Makerfabs/ESP32-S3-Parallel-TFT-with-Touch-4.3inch/examples/ESP-IDF/matouch/components/lvgl__lvgl/docs/src/_static/images/renesas/toolchains.png

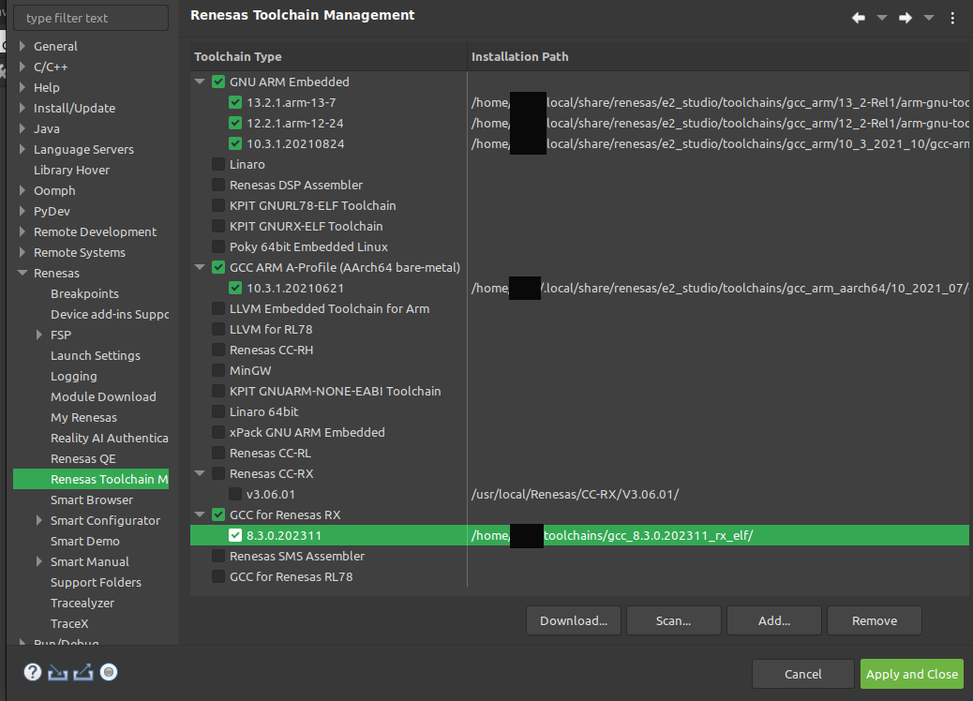
examples/ESP-IDF/matouch/components/lvgl__lvgl/docs/src/_static/images/renesas/toolchains.png
