Makerfabs/ESP32-S3-Parallel-TFT-with-Touch-4.3inch/examples/ESP-IDF/matouch/components/lvgl__lvgl/tests/ref_imgs/draw/render/al88/demo_render_box_shadow_opa_128.png

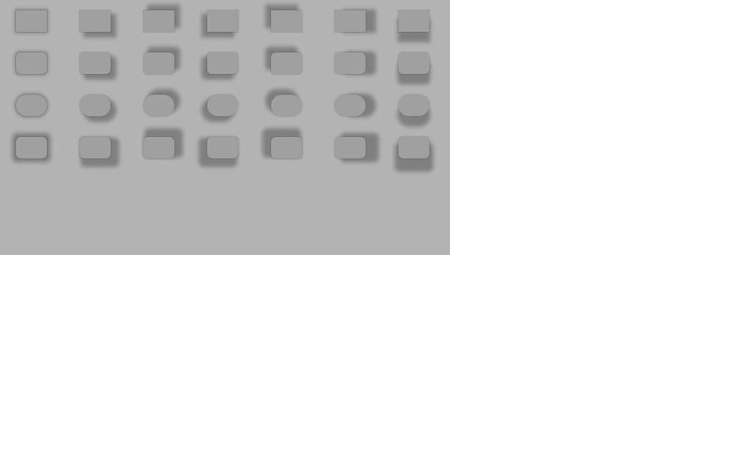
examples/ESP-IDF/matouch/components/lvgl__lvgl/tests/ref_imgs/draw/render/al88/demo_render_box_shadow_opa_128.png
