Makerfabs/ESP32-S3-Parallel-TFT-with-Touch-4.3inch/examples/ESP-IDF/matouch/components/lvgl__lvgl/tests/ref_imgs_vg_lite/draw/render/argb1555/demo_render_conical_gradient_opa_128.png

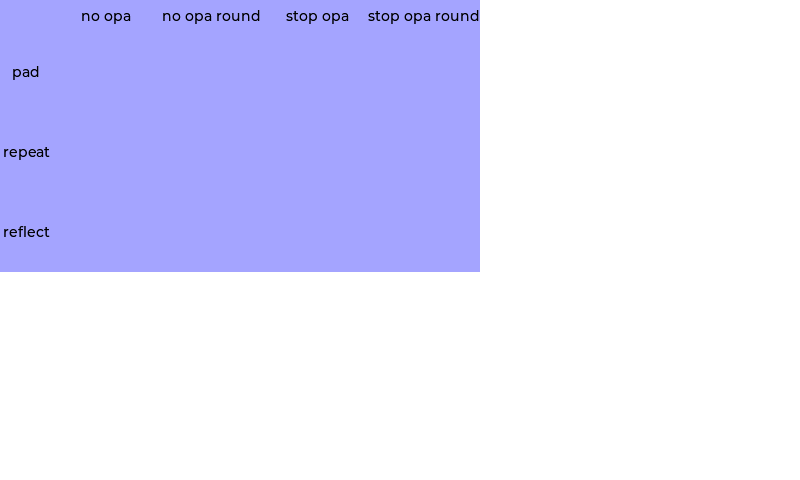
examples/ESP-IDF/matouch/components/lvgl__lvgl/tests/ref_imgs_vg_lite/draw/render/argb1555/demo_render_conical_gradient_opa_128.png
