Makerfabs/ESP32-S3-Parallel-TFT-with-Touch-4.3inch/examples/ESP-IDF/matouch/components/lvgl__lvgl/tests/ref_imgs_vg_lite/draw/render/argb2222/demo_render_triangle_opa_255.png

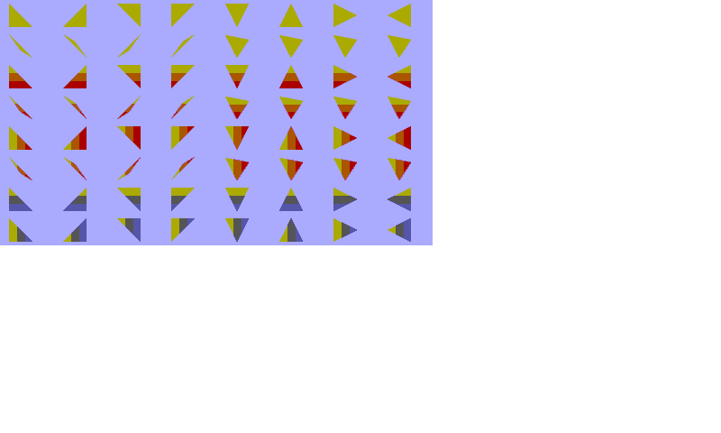
examples/ESP-IDF/matouch/components/lvgl__lvgl/tests/ref_imgs_vg_lite/draw/render/argb2222/demo_render_triangle_opa_255.png
