Makerfabs/ESP32-S3-Parallel-TFT-with-Touch-4.3inch/examples/LvglBenchmark/img_benchmark_cogwheel_alpha16.c

#include "lv_demo_benchmark.h"

#if LV_USE_DEMO_BENCHMARK

#ifndef LV_ATTRIBUTE_MEM_ALIGN
#define LV_ATTRIBUTE_MEM_ALIGN
#endif

#ifndef LV_ATTRIBUTE_IMG_IMG_COGWHEEL_ALPHA16
#define LV_ATTRIBUTE_IMG_IMG_COGWHEEL_ALPHA16
#endif

const LV_ATTRIBUTE_MEM_ALIGN LV_ATTRIBUTE_IMG_IMG_COGWHEEL_ALPHA16 uint8_t img_benchmark_cogwheel_alpha16_map[] = {
  0x00, 0x00, 0x00, 0x00, 0x00, 0x00, 0x00, 0x00, 0x00, 0x00, 0x00, 0x00, 0x00, 0x00, 0x00, 0x00, 0x00, 0x00, 0x00, 0x00, 0x00, 0x00, 0x00, 0xff, 0xff, 0xff, 0xf6, 0x00, 0x00, 0x00, 0x00, 0x00, 0x00, 0x00, 0x00, 0x00, 0x00, 0x00, 0x00, 0x00, 0x00, 0x00, 0x00, 0x00, 0x00, 0x00, 0x00, 0x00, 0x00, 0x00,
  0x00, 0x00, 0x00, 0x00, 0x00, 0x00, 0x00, 0x00, 0x00, 0x00, 0x00, 0x00, 0x00, 0x00, 0x00, 0x00, 0x00, 0x00, 0x00, 0x00, 0x00, 0x00, 0x01, 0xff, 0xff, 0xff, 0xff, 0x00, 0x00, 0x00, 0x00, 0x00, 0x00, 0x00, 0x00, 0x00, 0x00, 0x00, 0x00, 0x00, 0x00, 0x00, 0x00, 0x00, 0x00, 0x00, 0x00, 0x00, 0x00, 0x00,
  0x00, 0x00, 0x00, 0x00, 0x00, 0x00, 0x00, 0x00, 0x00, 0x00, 0x00, 0x00, 0x00, 0x00, 0x00, 0x00, 0x00, 0x00, 0x00, 0x00, 0x00, 0x00, 0x03, 0xff, 0xff, 0xff, 0xff, 0x00, 0x00, 0x00, 0x00, 0x05, 0xf2, 0x00, 0x00, 0x00, 0x00, 0x00, 0x00, 0x00, 0x00, 0x00, 0x00, 0x00, 0x00, 0x00, 0x00, 0x00, 0x00, 0x00,
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
};

const lv_img_dsc_t img_benchmark_cogwheel_alpha16 = {
  .header.always_zero = 0,
  .header.w = 100,
  .header.h = 100,
  .data_size = 5000,
  .header.cf = LV_IMG_CF_ALPHA_4BIT,
  .data = img_benchmark_cogwheel_alpha16_map,
};

#endif
