Makerfabs/ESP32-S3-Parallel-TFT-with-Touch-4.3inch/examples/LvglBenchmark/img_benchmark_cogwheel_rgb565a8.c

#include "lv_demo_benchmark.h"

#ifndef LV_ATTRIBUTE_MEM_ALIGN
#define LV_ATTRIBUTE_MEM_ALIGN
#endif

#ifndef LV_ATTRIBUTE_IMG_IMG_BENCHMARK_COGWHEEL_RGB565A8
#define LV_ATTRIBUTE_IMG_IMG_BENCHMARK_COGWHEEL_RGB565A8
#endif

const LV_ATTRIBUTE_MEM_ALIGN LV_ATTRIBUTE_LARGE_CONST LV_ATTRIBUTE_IMG_IMG_BENCHMARK_COGWHEEL_RGB565A8 uint8_t img_benchmark_cogwheel_rgb565a8_map[] = {
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

};

const lv_img_dsc_t img_benchmark_cogwheel_rgb565a8 = {
  .header.cf = LV_IMG_CF_RGB565A8,
  .header.always_zero = 0,
  .header.reserved = 0,
  .header.w = 100,
  .header.h = 100,
  .data_size = 30000,
  .data = img_benchmark_cogwheel_rgb565a8_map,
};
