Makerfabs/ESP32-S3-Parallel-TFT-with-Touch-4.3inch/examples/LvglBenchmark/lv_font_bechmark_montserrat_12_compr_az.c

#include "lv_demo_benchmark.h"

#if LV_USE_DEMO_BENCHMARK

/*******************************************************************************
 * Size: 12 px
 * Bpp: 4
 * Opts:
 ******************************************************************************/

#ifndef LV_FONT_BENCHMARK_MONTSERRAT_12_COMPR_AZ
#define LV_FONT_BENCHMARK_MONTSERRAT_12_COMPR_AZ 1
#endif

#if LV_FONT_BENCHMARK_MONTSERRAT_12_COMPR_AZ

/*-----------------
 *    BITMAPS
 *----------------*/

/*Store the image of the glyphs*/
static LV_ATTRIBUTE_LARGE_CONST const uint8_t gylph_bitmap[] = {
    /* U+20 " " */

    /* U+61 "a" */
    0x8, 0xdf, 0xc3, 0x0, 0x14, 0xea, 0xf0, 0x2,
    0x90, 0xa0, 0x84, 0x23, 0x7b, 0xc0, 0xd1, 0xb3,
    0xb8, 0x1, 0x84, 0x1c, 0x0, 0x8f, 0xdb, 0xe0,
    0x0,

    /* U+62 "b" */
    0xe4, 0x0, 0xff, 0xe4, 0x1e, 0x7e, 0x20, 0x2,
    0x27, 0x52, 0xc8, 0x25, 0x4a, 0x12, 0x80, 0x80,
    0x23, 0x20, 0x20, 0x8, 0xc8, 0x25, 0x4a, 0x12,
    0x82, 0x63, 0x52, 0xc8,

    /* U+63 "c" */
    0x2, 0xbf, 0xe8, 0x0, 0x78, 0xed, 0x21, 0xa8,
    0x51, 0x26, 0x19, 0x30, 0x7, 0x13, 0x0, 0x72,
    0x85, 0x12, 0x69, 0x87, 0x8e, 0xd2, 0x98,

    /* U+64 "d" */
    0x0, 0xe1, 0xf1, 0x0, 0xff, 0xe2, 0x95, 0xfe,
    0xb8, 0x5, 0x85, 0xbd, 0x60, 0x5, 0x39, 0x23,
    0x90, 0x1, 0x30, 0x4, 0xa0, 0x2, 0x60, 0x8,
    0x80, 0xa, 0x72, 0x25, 0xc0, 0x16, 0x17, 0x65,
    0x80, 0x0,

    /* U+65 "e" */
    0x2, 0xbf, 0xd5, 0x0, 0x61, 0xf4, 0xda, 0x29,
    0x40, 0xa4, 0x79, 0x1f, 0x75, 0xe, 0x44, 0xee,
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
    0x4, 0x33, 0xaa, 0xc0, 0x10,

    /* U+7A "z" */
    0x7f, 0xfd, 0x6f, 0xfe, 0xd0, 0x80, 0xb, 0xa0,
    0xc0, 0x12, 0xee, 0x0, 0x23, 0xd0, 0x0, 0x6a,
    0xc4, 0x1, 0x23, 0x5f, 0xed
};


/*---------------------
 *  GLYPH DESCRIPTION
 *--------------------*/

static const lv_font_fmt_txt_glyph_dsc_t glyph_dsc[] = {
    {.bitmap_index = 0, .adv_w = 0, .box_w = 0, .box_h = 0, .ofs_x = 0, .ofs_y = 0} /* id = 0 reserved */,
    {.bitmap_index = 0, .adv_w = 52, .box_w = 0, .box_h = 0, .ofs_x = 0, .ofs_y = 0},
    {.bitmap_index = 0, .adv_w = 115, .box_w = 7, .box_h = 7, .ofs_x = 0, .ofs_y = 0},
    {.bitmap_index = 25, .adv_w = 131, .box_w = 7, .box_h = 10, .ofs_x = 1, .ofs_y = 0},
    {.bitmap_index = 53, .adv_w = 110, .box_w = 7, .box_h = 7, .ofs_x = 0, .ofs_y = 0},
    {.bitmap_index = 76, .adv_w = 131, .box_w = 8, .box_h = 10, .ofs_x = 0, .ofs_y = 0},
    {.bitmap_index = 110, .adv_w = 118, .box_w = 7, .box_h = 7, .ofs_x = 0, .ofs_y = 0},
    {.bitmap_index = 134, .adv_w = 68, .box_w = 5, .box_h = 10, .ofs_x = 0, .ofs_y = 0},
    {.bitmap_index = 150, .adv_w = 132, .box_w = 8, .box_h = 10, .ofs_x = 0, .ofs_y = -3},
    {.bitmap_index = 190, .adv_w = 131, .box_w = 7, .box_h = 10, .ofs_x = 1, .ofs_y = 0},
    {.bitmap_index = 214, .adv_w = 54, .box_w = 3, .box_h = 10, .ofs_x = 0, .ofs_y = 0},
    {.bitmap_index = 224, .adv_w = 55, .box_w = 5, .box_h = 13, .ofs_x = -2, .ofs_y = -3},
    {.bitmap_index = 241, .adv_w = 118, .box_w = 7, .box_h = 10, .ofs_x = 1, .ofs_y = 0},
    {.bitmap_index = 265, .adv_w = 54, .box_w = 2, .box_h = 10, .ofs_x = 1, .ofs_y = 0},
    {.bitmap_index = 270, .adv_w = 203, .box_w = 11, .box_h = 7, .ofs_x = 1, .ofs_y = 0},
    {.bitmap_index = 296, .adv_w = 131, .box_w = 7, .box_h = 7, .ofs_x = 1, .ofs_y = 0},
    {.bitmap_index = 316, .adv_w = 122, .box_w = 8, .box_h = 7, .ofs_x = 0, .ofs_y = 0},
    {.bitmap_index = 344, .adv_w = 131, .box_w = 7, .box_h = 10, .ofs_x = 1, .ofs_y = -3},
    {.bitmap_index = 375, .adv_w = 131, .box_w = 8, .box_h = 10, .ofs_x = 0, .ofs_y = -3},
    {.bitmap_index = 409, .adv_w = 79, .box_w = 4, .box_h = 7, .ofs_x = 1, .ofs_y = 0},
    {.bitmap_index = 420, .adv_w = 96, .box_w = 6, .box_h = 7, .ofs_x = 0, .ofs_y = 0},
    {.bitmap_index = 442, .adv_w = 79, .box_w = 5, .box_h = 9, .ofs_x = 0, .ofs_y = 0},
    {.bitmap_index = 460, .adv_w = 130, .box_w = 7, .box_h = 7, .ofs_x = 1, .ofs_y = 0},
    {.bitmap_index = 478, .adv_w = 107, .box_w = 8, .box_h = 7, .ofs_x = -1, .ofs_y = 0},
    {.bitmap_index = 505, .adv_w = 173, .box_w = 11, .box_h = 7, .ofs_x = 0, .ofs_y = 0},
    {.bitmap_index = 545, .adv_w = 106, .box_w = 7, .box_h = 7, .ofs_x = 0, .ofs_y = 0},
    {.bitmap_index = 570, .adv_w = 107, .box_w = 8, .box_h = 10, .ofs_x = -1, .ofs_y = -3},
    {.bitmap_index = 607, .adv_w = 100, .box_w = 6, .box_h = 7, .ofs_x = 0, .ofs_y = 0}
};

/*---------------------
 *  CHARACTER MAPPING
 *--------------------*/



/*Collect the unicode lists and glyph_id offsets*/
static const lv_font_fmt_txt_cmap_t cmaps[] =
{
    {
        .range_start = 32, .range_length = 1, .glyph_id_start = 1,
        .unicode_list = NULL, .glyph_id_ofs_list = NULL, .list_length = 0, .type = LV_FONT_FMT_TXT_CMAP_FORMAT0_TINY
    },
    {
        .range_start = 97, .range_length = 26, .glyph_id_start = 2,
        .unicode_list = NULL, .glyph_id_ofs_list = NULL, .list_length = 0, .type = LV_FONT_FMT_TXT_CMAP_FORMAT0_TINY
    }
};

/*-----------------
 *    KERNING
 *----------------*/


/*Map glyph_ids to kern left classes*/
static const uint8_t kern_left_class_mapping[] =
{
    0, 0, 1, 2, 3, 4, 5, 6,
    0, 1, 0, 0, 7, 4, 1, 1,
    2, 2, 8, 9, 10, 11, 0, 12,
    12, 13, 12, 14
};

/*Map glyph_ids to kern right classes*/
static const uint8_t kern_right_class_mapping[] =
{
    0, 0, 1, 2, 3, 3, 3, 0,
    3, 2, 4, 5, 2, 2, 4, 4,
    3, 4, 3, 4, 6, 7, 8, 9,
    9, 10, 9, 11
};

/*Kern values between classes*/
static const int8_t kern_class_values[] =
{
    0, 0, 1, 0, 0, 0, 0, 0,
    -2, 0, 0, -1, 0, 0, 0, 0,
    0, 0, 0, -3, -3, -2, 0, -1,
    -2, 0, 0, 0, 1, 0, -1, -3,
    -1, 0, 0, 0, 0, 0, 0, 2,
    0, 0, 0, 0, -3, 0, 0, 0,
    0, 0, 0, 0, -2, -3, -1, -2,
    0, -2, 15, 8, 0, 0, 0, 2,
    0, 0, -2, 0, -4, -1, 0, -3,
    0, -2, -5, -4, -2, 0, 0, 0,
    0, 10, 0, 0, 0, 0, 0, 0,
    -2, -1, -2, -1, 0, -1, 3, 0,
    3, -1, 0, 0, 0, 0, 0, 0,
    0, 0, 0, -2, -2, 0, 0, 0,
    -3, 0, 0, 0, -2, 0, -2, 0,
    0, -3, 0, -3, 0, -3, -1, 3,
    0, -2, -6, -2, -2, 0, -3, 0,
    1, -2, 0, -2, -6, 0, -2, 0,
    0, -2, 0, 0, 0, 0, 0, -2,
    -2, 0
};


/*Collect the kern class' data in one place*/
static const lv_font_fmt_txt_kern_classes_t kern_classes =
{
    .class_pair_values   = kern_class_values,
    .left_class_mapping  = kern_left_class_mapping,
    .right_class_mapping = kern_right_class_mapping,
    .left_class_cnt      = 14,
    .right_class_cnt     = 11,
};

/*--------------------
 *  ALL CUSTOM DATA
 *--------------------*/

/*Store all the custom data of the font*/
static lv_font_fmt_txt_dsc_t font_dsc = {
    .glyph_bitmap = gylph_bitmap,
    .glyph_dsc = glyph_dsc,
    .cmaps = cmaps,
    .kern_dsc = &kern_classes,
    .kern_scale = 16,
    .cmap_num = 2,
    .bpp = 4,
    .kern_classes = 1,
    .bitmap_format = 1
};


/*-----------------
 *  PUBLIC FONT
 *----------------*/

/*Initialize a public general font descriptor*/
lv_font_t lv_font_benchmark_montserrat_12_compr_az = {
    .get_glyph_dsc = lv_font_get_glyph_dsc_fmt_txt,    /*Function pointer to get glyph's data*/
    .get_glyph_bitmap = lv_font_get_bitmap_fmt_txt,    /*Function pointer to get glyph's bitmap*/
    .line_height = 13,          /*The maximum line height required by the font*/
    .base_line = 3,             /*Baseline measured from the bottom of the line*/
#if !(LVGL_VERSION_MAJOR == 6 && LVGL_VERSION_MINOR == 0)
    .subpx = LV_FONT_SUBPX_NONE,
#endif
    .dsc = &font_dsc           /*The custom font data. Will be accessed by `get_glyph_bitmap/dsc` */
};

#endif /*#if LV_FONT_BENCHMARK_MONTSERRAT_12_COMPR_AZ*/

#endif
