Makerfabs/ESP32-S3-Parallel-TFT-with-Touch-4.3inch/examples/LvglWidgets/img_clothes.c

#include "lv_demo_widgets.h"

#if LV_USE_DEMO_WIDGETS

#ifndef LV_ATTRIBUTE_MEM_ALIGN
#define LV_ATTRIBUTE_MEM_ALIGN
#endif

#ifndef LV_ATTRIBUTE_IMG_IMG_CLOTHES
#define LV_ATTRIBUTE_IMG_IMG_CLOTHES
#endif

const LV_ATTRIBUTE_MEM_ALIGN LV_ATTRIBUTE_LARGE_CONST LV_ATTRIBUTE_IMG_IMG_CLOTHES uint8_t img_clothes_map[] = {
#if LV_COLOR_DEPTH == 1 || LV_COLOR_DEPTH == 8
  /*Pixel format: Blue: 2 bit, Green: 3 bit, Red: 3 bit, Alpha 8 bit */
  0xff, 0x00, 0xff, 0x00, 0xff, 0x00, 0xff, 0x00, 0xff, 0x00, 0xff, 0x07, 0xff, 0x50, 0xff, 0x9b, 0xff, 0xd0, 0xff, 0xe8, 0xff, 0xef, 0xff, 0xef, 0xff, 0xef, 0xff, 0xef, 0xff, 0xef, 0xff, 0xef, 0xff, 0xef, 0xff, 0xef, 0xd7, 0xef, 0xd2, 0xef, 0x8d, 0xef, 0x8d, 0xef, 0xd6, 0xef, 0xfb, 0xef, 0xff, 0xef, 0xff, 0xef, 0xfb, 0xef, 0xfb, 0xef, 0xff, 0xef, 0xff, 0xef, 0xfb, 0xef, 0xff, 0xef, 0xff, 0xef, 0xff, 0xef, 0xff, 0xef, 0xff, 0xef, 0xff, 0xef, 0xff, 0xef, 0xff, 0xef, 0xff, 0xef, 0xff, 0xef, 0xff, 0xef, 0xff, 0xef, 0xff, 0xef, 0xff, 0xef, 0xff, 0xef, 0xff, 0xe3, 0xff, 0xc8, 0xff, 0x9b, 0xff, 0x4f, 0xff, 0x07, 0xff, 0x00, 0xff, 0x00, 0xff, 0x00, 0xff, 0x00, 0xff, 0x00,
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
