Makerfabs/ESP32-S3-Parallel-TFT-with-Touch-4.3inch/examples/LvglWidgets/img_lvgl_logo.c

#include "lv_demo_widgets.h"

#if LV_USE_DEMO_WIDGETS

#ifndef LV_ATTRIBUTE_MEM_ALIGN
#define LV_ATTRIBUTE_MEM_ALIGN
#endif

#ifndef LV_ATTRIBUTE_IMG_IMG_LVGL_LOGO
#define LV_ATTRIBUTE_IMG_IMG_LVGL_LOGO
#endif

const LV_ATTRIBUTE_MEM_ALIGN LV_ATTRIBUTE_LARGE_CONST LV_ATTRIBUTE_IMG_IMG_LVGL_LOGO uint8_t img_lvgl_logo_map[] = {
#if LV_COLOR_DEPTH == 1 || LV_COLOR_DEPTH == 8
  /*Pixel format: Blue: 2 bit, Green: 3 bit, Red: 3 bit, Alpha 8 bit */
  0xff, 0xff, 0xff, 0xff, 0xff, 0xff, 0xff, 0xff, 0xff, 0xff, 0xdb, 0xff, 0xdb, 0xff, 0xdb, 0xff, 0xdb, 0xff, 0xdb, 0xff, 0xdb, 0xff, 0xdb, 0xff, 0xdb, 0xff, 0xdb, 0xff, 0xdb, 0xff, 0xdb, 0xff, 0xdb, 0xff, 0xdb, 0xff, 0xdb, 0xff, 0xdb, 0xff, 0xdb, 0xff, 0xdb, 0xff, 0xdb, 0xff, 0xdb, 0xff, 0xdb, 0xff, 0xdb, 0xff, 0xdb, 0xff, 0xdb, 0xff, 0xdb, 0xff, 0xdb, 0xff, 0xdb, 0xff, 0xdb, 0xff, 0xdb, 0xff, 0xdb, 0xff, 0xdb, 0xff, 0xdb, 0xff, 0xff, 0xff, 0xff, 0xff, 0xff, 0xff, 0xff, 0xff, 0xff, 0xff, 0xff, 0xff,
  0xff, 0xff, 0xff, 0xff, 0xb7, 0xff, 0x6e, 0xff, 0x6d, 0xff, 0x6d, 0xff, 0x6d, 0xff, 0x6d, 0xff, 0x6d, 0xff, 0x6d, 0xff, 0x6d, 0xff, 0x6d, 0xff, 0x6d, 0xff, 0x6d, 0xff, 0x6d, 0xff, 0x6d, 0xff, 0x6d, 0xff, 0x6d, 0xff, 0x6d, 0xff, 0x6d, 0xff, 0x6d, 0xff, 0x6d, 0xff, 0x6d, 0xff, 0x6d, 0xff, 0x6d, 0xff, 0x6d, 0xff, 0x6d, 0xff, 0x6d, 0xff, 0x6d, 0xff, 0x6d, 0xff, 0x6d, 0xff, 0x6d, 0xff, 0x6d, 0xff, 0x6d, 0xff, 0x6d, 0xff, 0x6d, 0xff, 0x6d, 0xff, 0x6e, 0xff, 0xb6, 0xff, 0xdb, 0xff, 0xff, 0xff, 0xff, 0xff,
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
