Makerfabs/ESP32-S3-Parallel-TFT-with-Touch-4.3inch/examples/ESP-IDF/squareline/components/bsp/audio/no_audio_codec.c

#include "no_audio_codec.h"

#include <esp_log.h>
#include <esp_check.h>
#include <esp_heap_caps.h>
#include <freertos/FreeRTOS.h>


#include "bsp_config.h"

#define TAG "audio"

static i2s_chan_handle_t _tx_handle = NULL;
static i2s_chan_handle_t _rx_handle = NULL;


// @brief read&write buffer

void no_audio_codec_simplex(audio_cfg_t *config)
{
    // Create a new channel for speaker
    i2s_chan_config_t chan_cfg = {
        .id = I2S_NUM_0,
        .role = I2S_ROLE_MASTER,
        .dma_desc_num = 6,
        .dma_frame_num = 240,
        .auto_clear_after_cb = true,
        .auto_clear_before_cb = false,
        .allow_pd = false,
        .intr_priority = 0,
    };
    ESP_ERROR_CHECK(i2s_new_channel(&chan_cfg, &_tx_handle, NULL));

    i2s_std_config_t std_cfg = {
        .clk_cfg = I2S_STD_CLK_DEFAULT_CONFIG(config->input_sample_rate),
        .slot_cfg = {
            .data_bit_width = I2S_DATA_BIT_WIDTH_32BIT,
            .slot_bit_width = AUDIO_DATA_BIT_WIDTH,
            .slot_mode = I2S_SLOT_MODE_MONO,
            .slot_mask = config->spk_slot_mask,
            .ws_width = I2S_DATA_BIT_WIDTH_32BIT,
            .ws_pol = false,
            .bit_shift = false,
            #if SOC_I2S_HW_VERSION_2
            .left_align = false,
            .big_endian = false,
            .bit_order_lsb = false
            #endif

        },
        .gpio_cfg = {
            .mclk = I2S_GPIO_UNUSED,
            .bclk = config->spk_bclk,
            .ws = config->spk_ws,
            .dout = config->spk_dout,
            .din = I2S_GPIO_UNUSED,
            .invert_flags = {
                .mclk_inv = false,
                .bclk_inv = false,
                .ws_inv = false
            }
        }
    };
    ESP_ERROR_CHECK(i2s_channel_init_std_mode(_tx_handle, &std_cfg));

    // Create a new channel for MIC
    chan_cfg.id = I2S_NUM_1;
    ESP_ERROR_CHECK(i2s_new_channel(&chan_cfg, NULL, &_rx_handle));
    std_cfg.clk_cfg.sample_rate_hz = (uint32_t)config->input_sample_rate;
    std_cfg.slot_cfg.slot_mask = config->mic_slot_mask;
    std_cfg.gpio_cfg.bclk = config->mic_sck;
    std_cfg.gpio_cfg.ws = config->mic_ws;
    std_cfg.gpio_cfg.dout = I2S_GPIO_UNUSED;
    std_cfg.gpio_cfg.din = config->mic_din;
    ESP_ERROR_CHECK(i2s_channel_init_std_mode(_rx_handle, &std_cfg));

    if(_tx_handle != NULL) i2s_channel_enable(_tx_handle);
    if(_rx_handle != NULL) i2s_channel_enable(_rx_handle);

    ESP_LOGI(TAG, "Simplex channels created");
}
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
